sunliguo2020/mono_4_2TFT_ESP32C3/components/sleep/include/sleep.h

#pragma once

#ifdef __cplusplus
extern "C" {
#endif

typedef void (*sleep_update_cb_t)(void);

// Create the sleep task (idempotent).
void sleep_init(void);
// Start the light-sleep loop.
void sleep_start_light(void);

// Hooks for future expansion.
void sleep_register_battery_update_cb(sleep_update_cb_t cb);
// Notify IO5 wake.
void sleep_notify_io5_wake(void);

#ifdef __cplusplus
}
#endif
