sunliguo2020/mono_4_2TFT_ESP32C3/components/board_mono_tft/include/MONO_TFT.h

#pragma once

#define TE_PIN  1
#define RST_PIN 20
#define DC_PIN  10
#define CS_PIN  -1
#define SCLK_PIN 4
#define SDI_PIN  6

#define TFT_WIDTH  300
#define TFT_HEIGHT 400
